MartinDejmal/PrusaCupHeater/Pictures/IMG_0198.jpeg

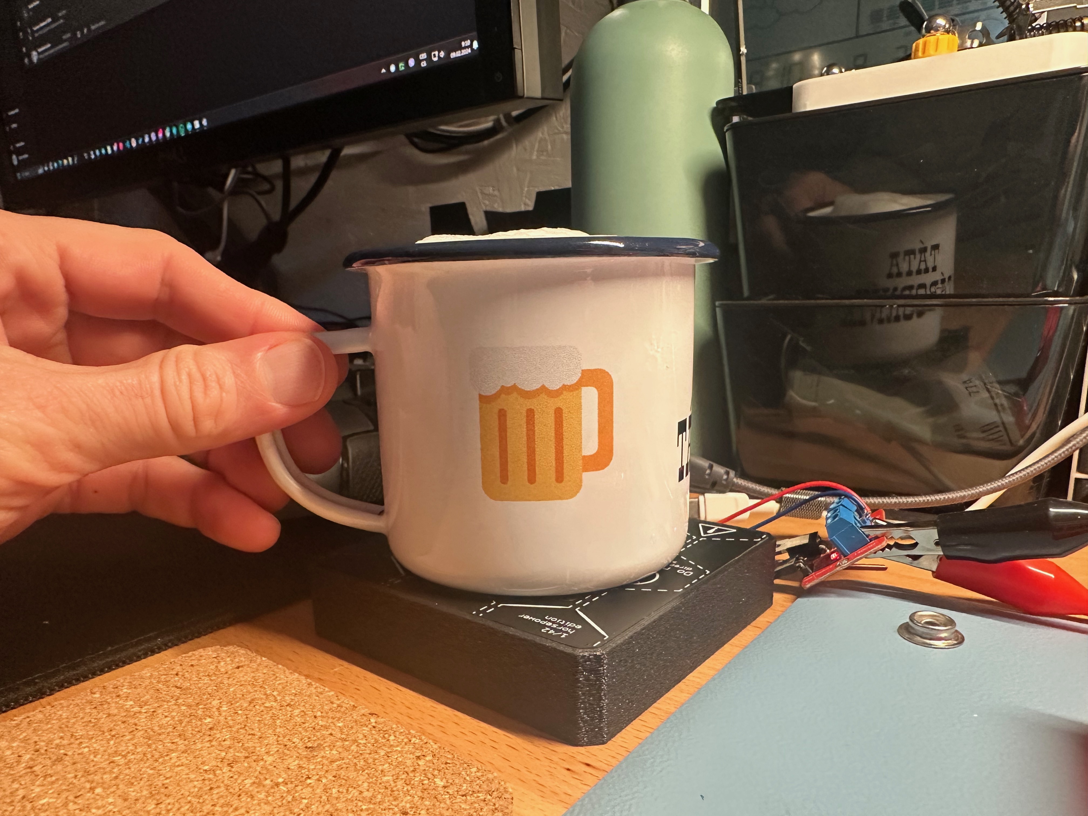
Pictures/IMG_0198.jpeg
