MartinDejmal/PrusaCupHeater/Pictures/IMG_0201.jpeg

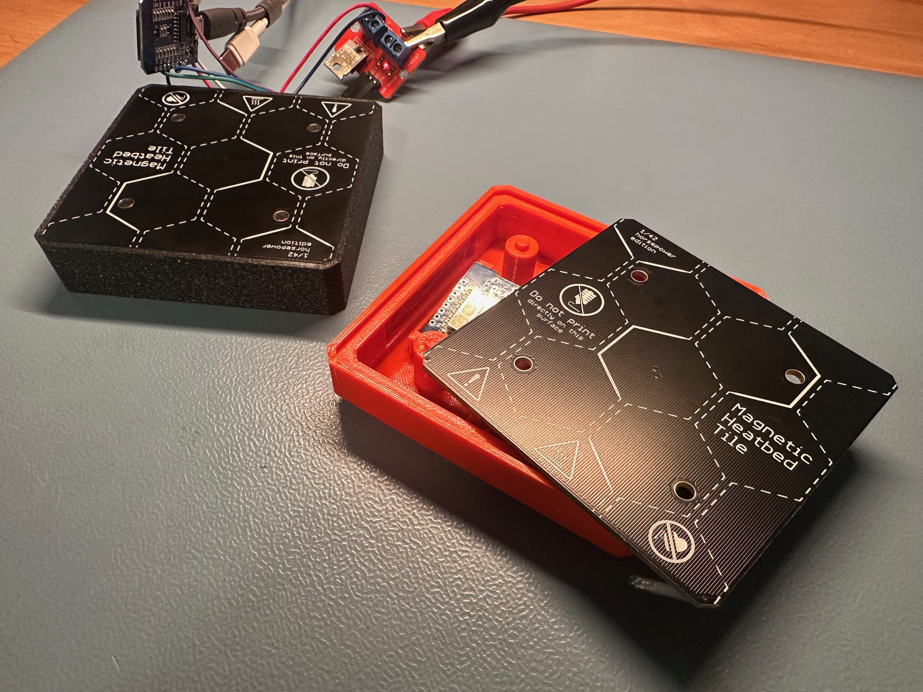
Pictures/IMG_0201.jpeg
